GuitarML/FunBox/software/images/saturn_infographic.jpg

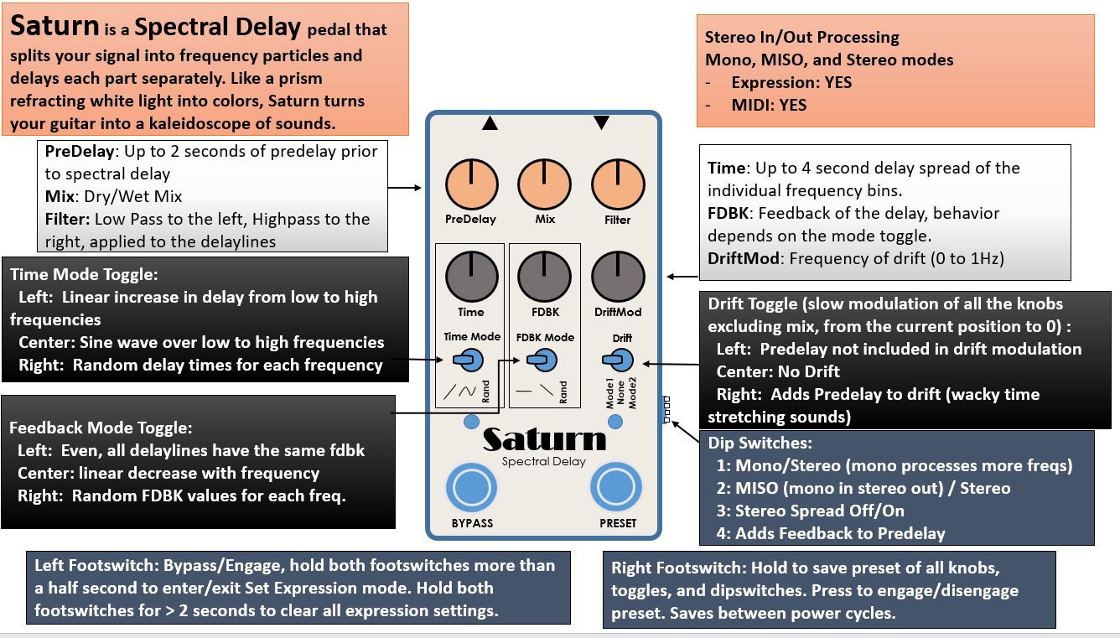
software/images/saturn_infographic.jpg
